pab-h/dolphin/firmware/include/constants.hpp

#ifndef CONSTANTS_HEADER 

#define CONSTANTS_HEADER

#define SECONDS_TO_MICROSECONDS 1000000
#define MICROSECONDS_TO_SECOUNDS .000001

#define SECONDS_TO_HOURS        .000277777777 


#define CENTIMETERS_TO_KILOMETERS .00001 

#endif
