pab-h/dolphin/firmware/src/System.cpp

#include <Arduino.h>
#include <EEPROM.h>
#include "System.hpp"

System* System::instance = nullptr;

System::System() {

    this->radius = EEPROM.read(RADIUS_EEPROM_ADDRESS);

    this->hallSensor = new HallSensor();

    this->speedometer = new Speedometer(this->radius);
    this->hodometer   = new Hodometer(this->radius);

    this->speedDisplay    = new SpeedDisplay(this->speedometer);
    this->distanceDisplay = new DistanceDisplay(this->hodometer);
    this->configDisplay   = new ConfigDisplay(&this->radius);

    this->leftButton  = new PushButtonSensor(LEFT_BUTTON_PIN);
    this->rightButton = new PushButtonSensor(RIGHT_BUTTON_PIN);

    this->lastConfigState = false;
    this->configState     = false;

}

System& System::getInstance() {

    if (!System::instance) {
        System::instance = new System();
    }

    return *System::instance;

}

System::~System() {

    delete hallSensor;
    delete speedometer;
    delete hodometer;
    delete speedDisplay;
    delete distanceDisplay;
    delete leftButton;
    delete rightButton;
    
    if (System::instance == this) {
        System::instance = nullptr;
    }

}

void System::setupListeners() {

    this->leftButton->addLongPressListener(System::staticToggleConfigMode);
    
    this->leftButton->addClickListener(System::staticOnLeftClick);
    this->rightButton->addClickListener(System::staticOnRightClick);

}

void System::setupDisplays() {

    this->distanceDisplay->setup();
    this->speedDisplay->setup();

}

void System::ISRHallSensorHit() {

    this->speedometer->ISRHallSensorHit();
    this->hodometer->ISRHallSensorHit();

}

void System::toggleConfigMode() {

    this->lastConfigState = configState;
    this->configState = !configState;

    if (this->configState) {
        this->configDisplay->setup();
    }

    if (this->lastConfigState && !this->configState) {

        EEPROM.write(RADIUS_EEPROM_ADDRESS, this->radius);

        this->hodometer->setRadius(this->radius);
        this->speedometer->setRadius(this->radius);

        this->configDisplay->done();
        delay(500);

    }

}

void System::onLeftClick() {

    if (!this->configState) {
        return;
    }

    this->radius++;

}

void System::onRightClick() {


    if (this->configState) {

        if (this->radius == 1) {
            return;
        }

        this->radius--;

        return;
    }

    this->hodometer->reset();

}

void System::run() {

    this->leftButton->read();
    this->rightButton->read();
    
    if (this->configState) {

        this->configDisplay->update();
        return;

    } 
    
    this->distanceDisplay->update();
    this->speedDisplay->update();

    this->speedometer->resetTrigger();

}
